stojnev/technics-balanced/Photographs/3d_bracket_2.jpg

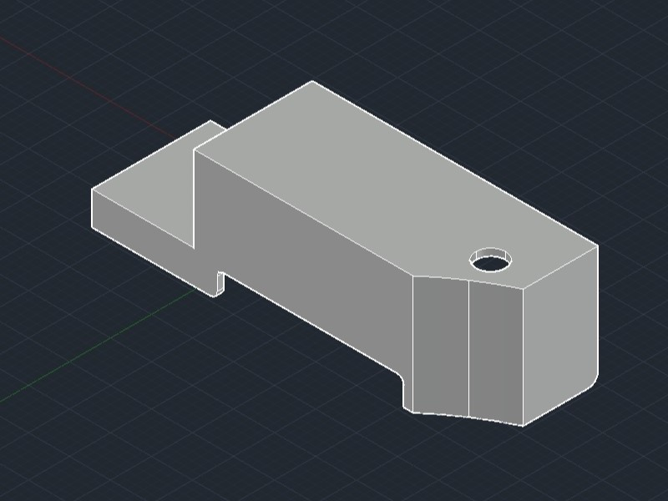
Photographs/3d_bracket_2.jpg
