stojnev/technics-balanced/Photographs/image_1.jpg

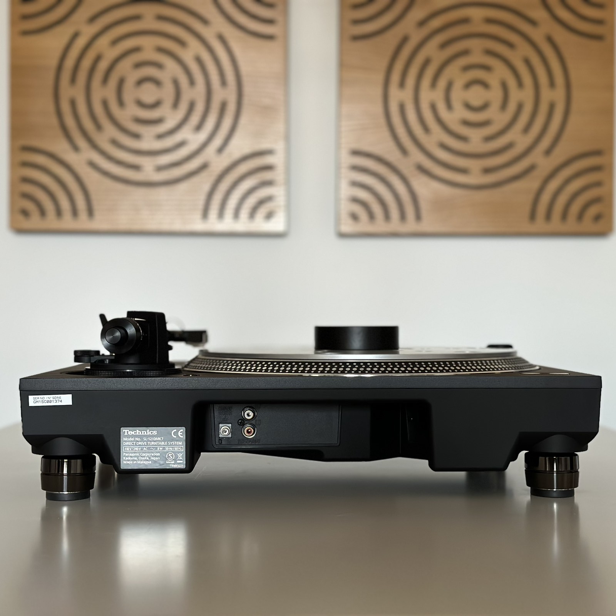
Photographs/image_1.jpg
