stojnev/technics-balanced/Photographs/image_2.jpg

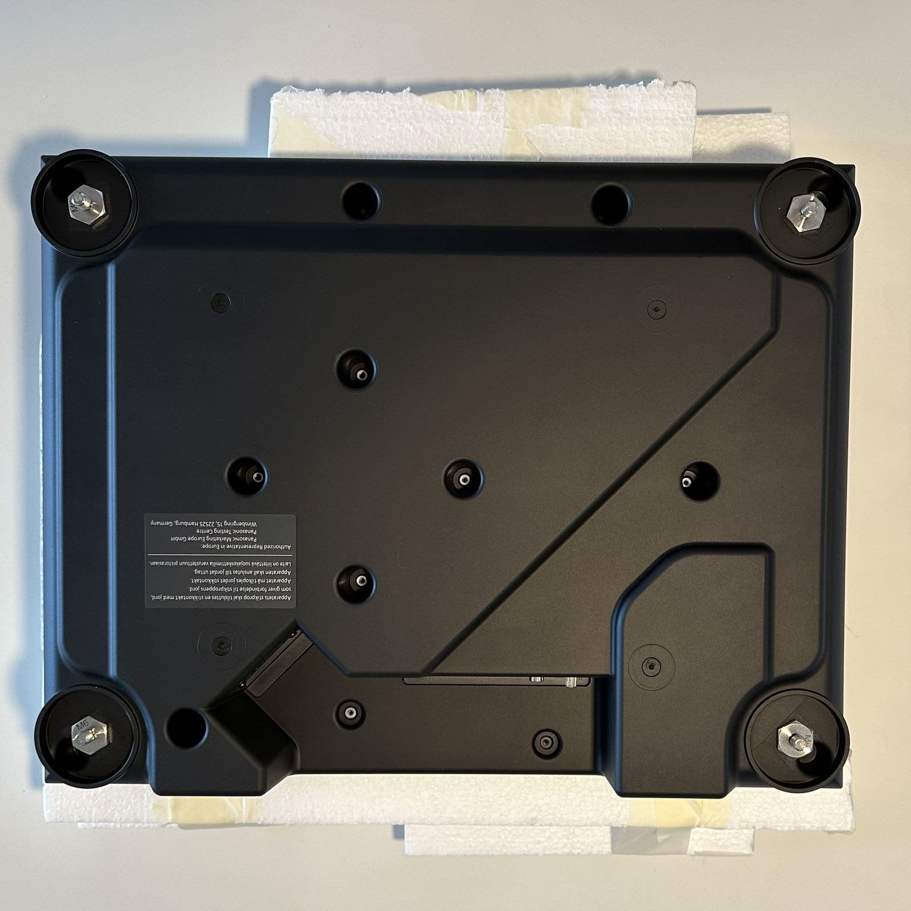
Photographs/image_2.jpg
