stojnev/technics-balanced/Photographs/image_4.jpg

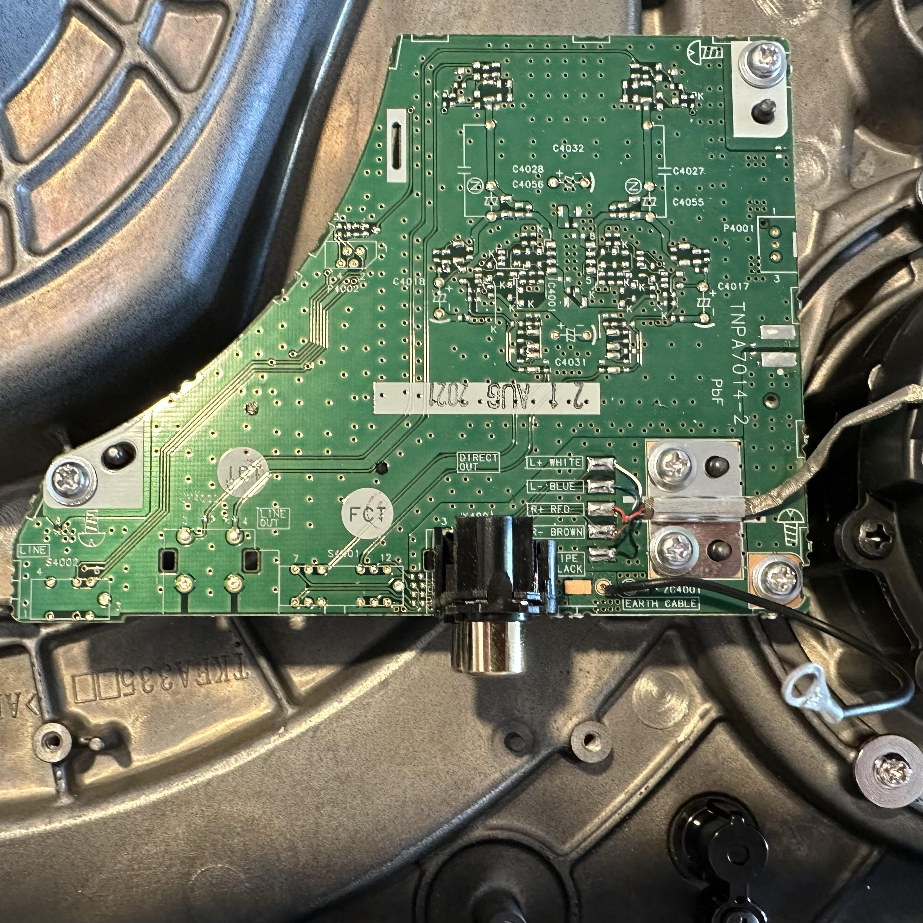
Photographs/image_4.jpg
