stojnev/technics-balanced/Photographs/image_5.jpg

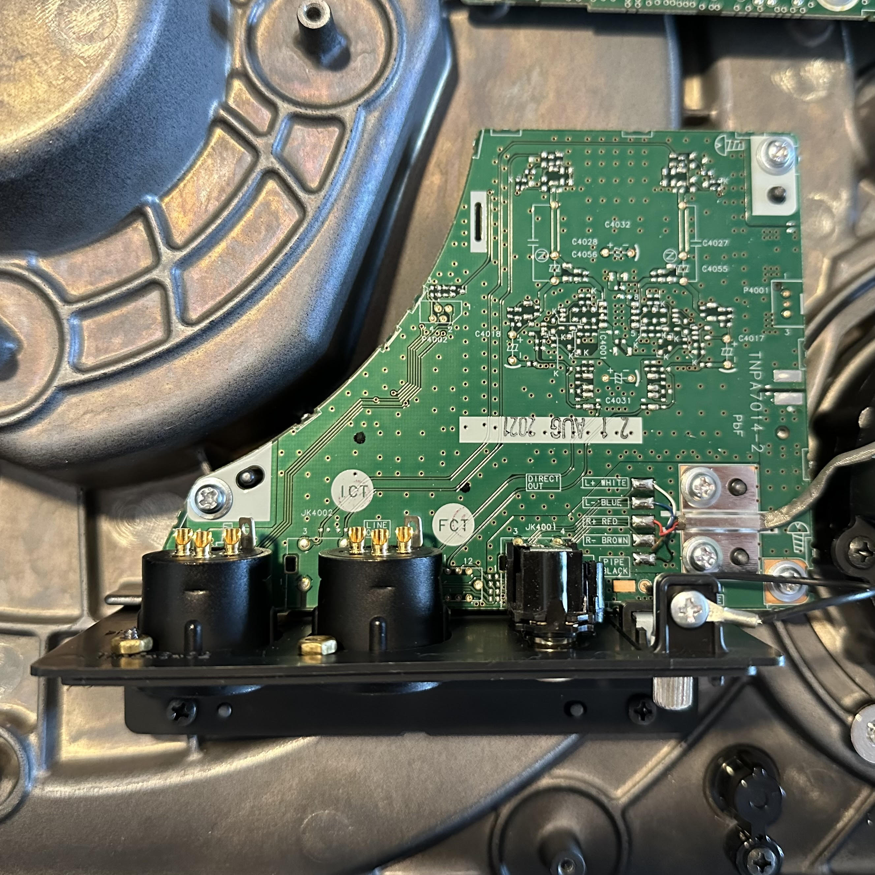
Photographs/image_5.jpg
