stojnev/technics-balanced/Photographs/image_6.jpg

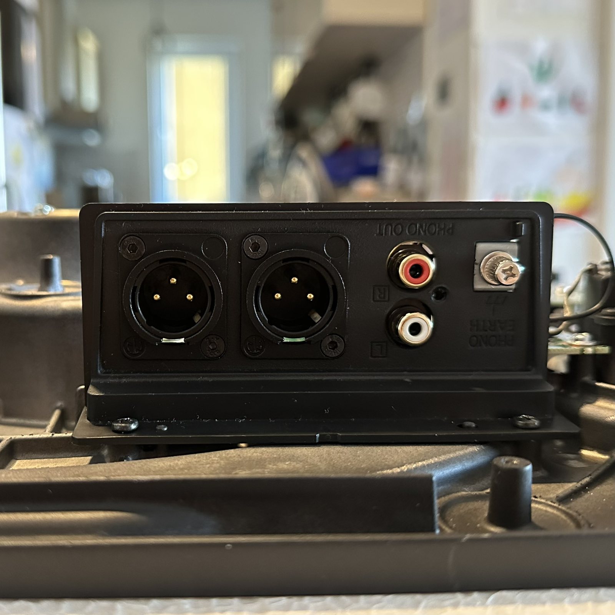
Photographs/image_6.jpg
