stojnev/technics-balanced/Photographs/image_7.jpg

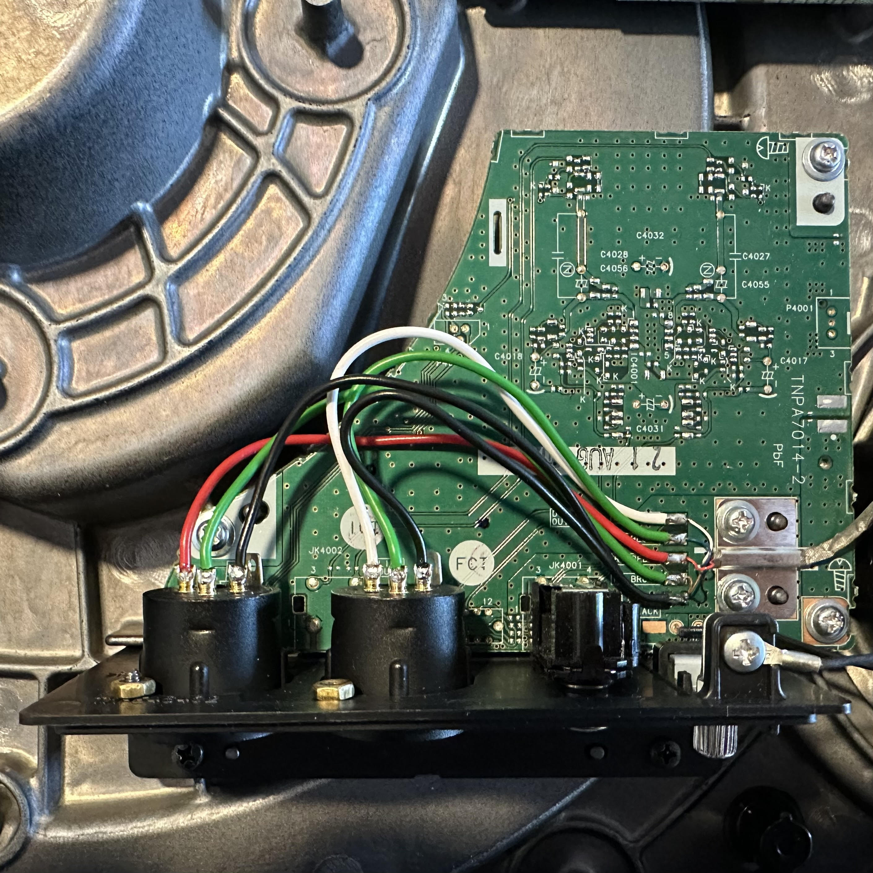
Photographs/image_7.jpg
