stojnev/technics-balanced/Photographs/image_8.jpg

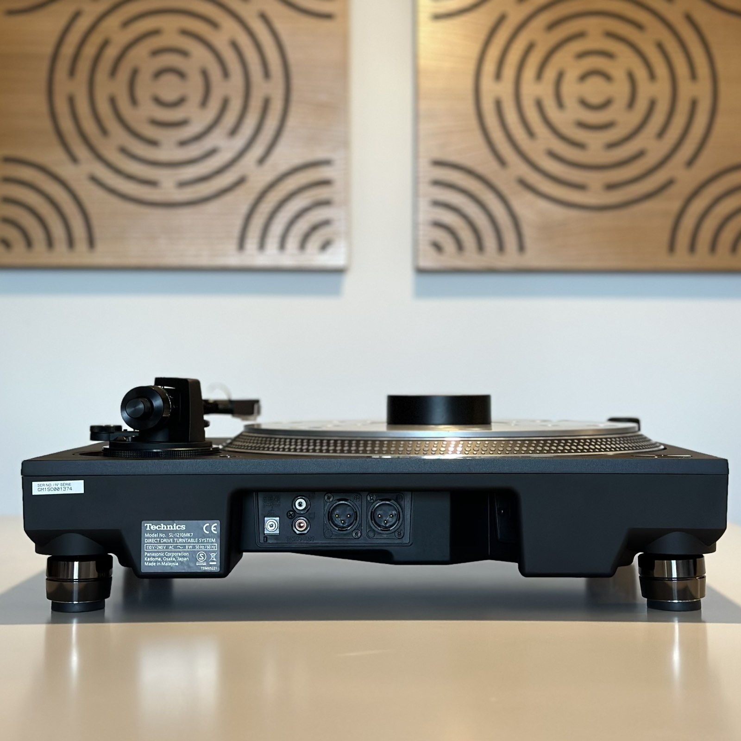
Photographs/image_8.jpg
