stojnev/technics-balanced/Photographs/plastic_bracket_blank.jpg

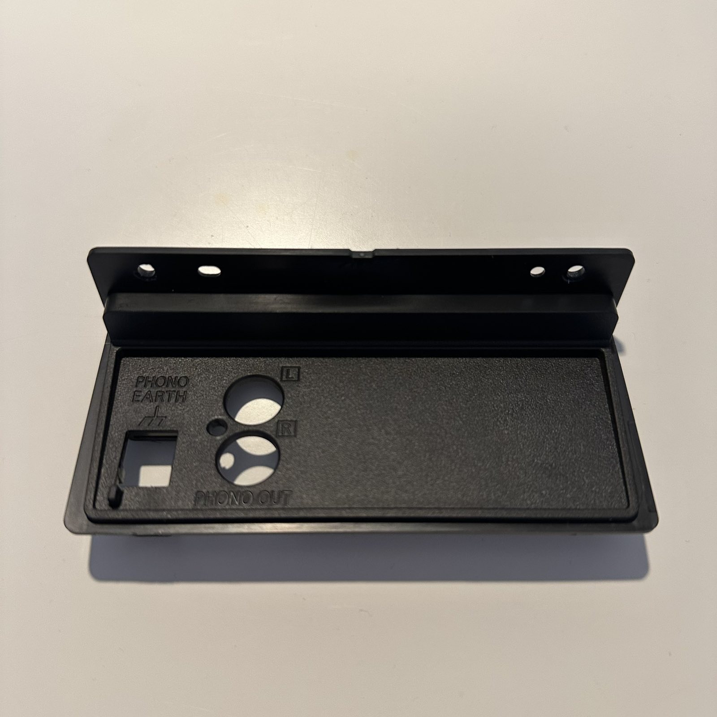
Photographs/plastic_bracket_blank.jpg
