stojnev/technics-balanced/Photographs/screening_can.jpg

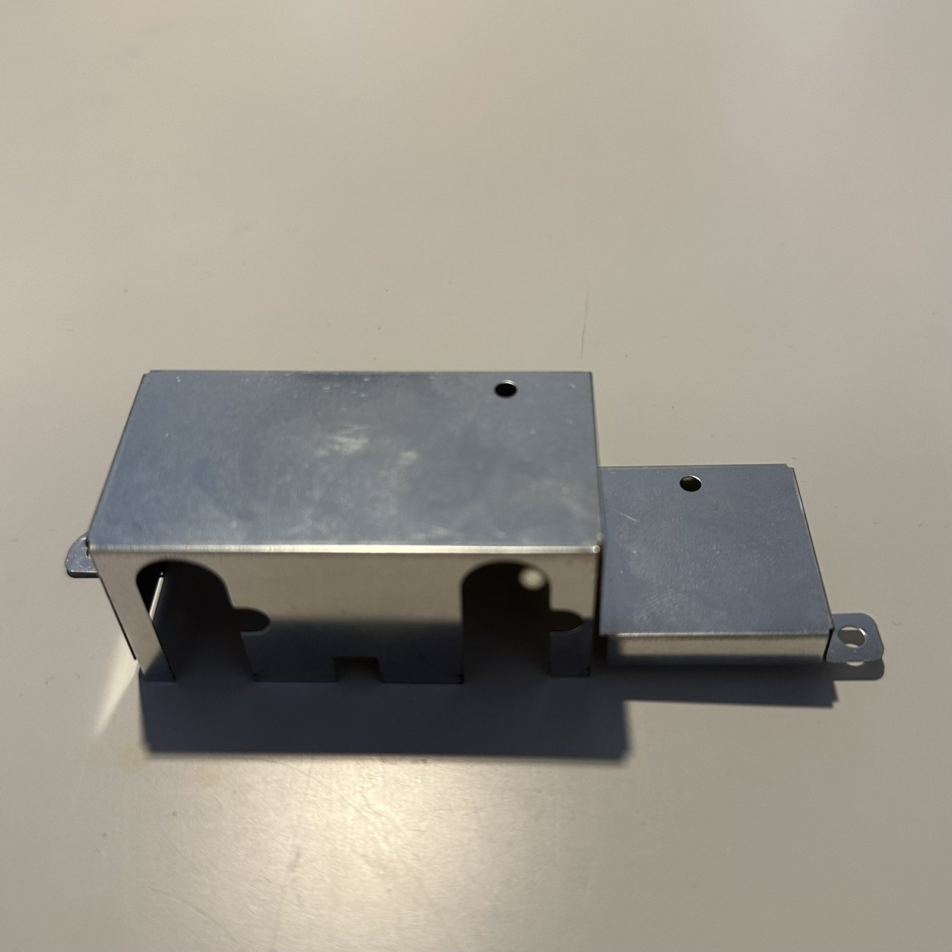
Photographs/screening_can.jpg
