stojnev/technics-balanced/Diagrams/xlr_wiring_diagram.jpg

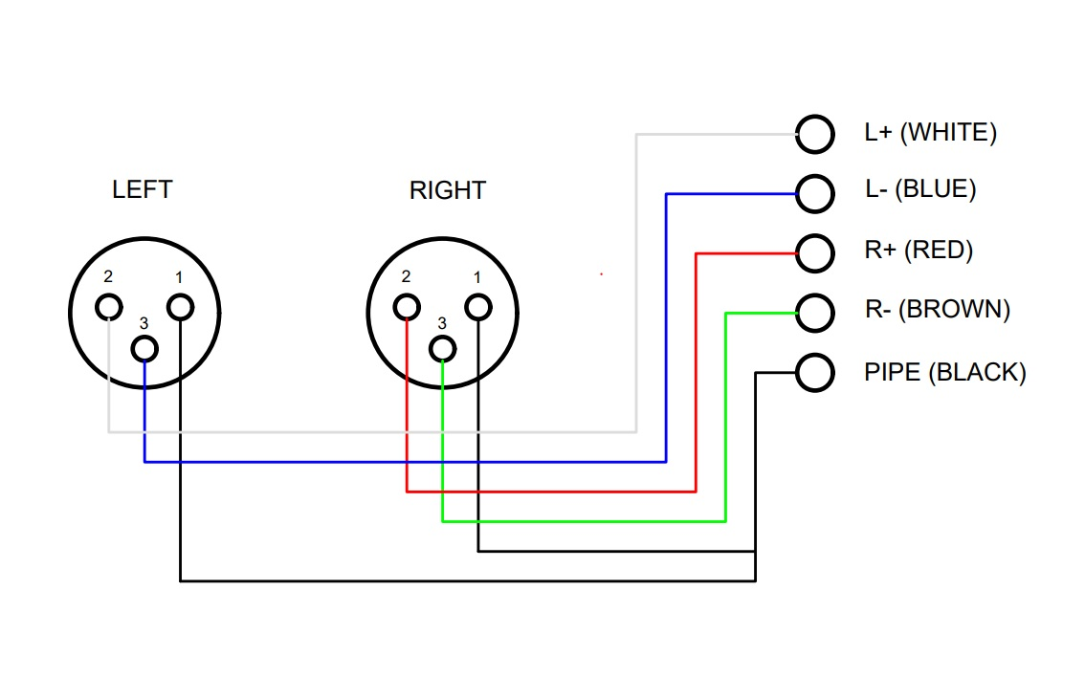
Diagrams/xlr_wiring_diagram.jpg
